ponderononon/IEMU_DevBoards/IEMU_Shared_Libraries/3D/TMUX1204DQAR.step

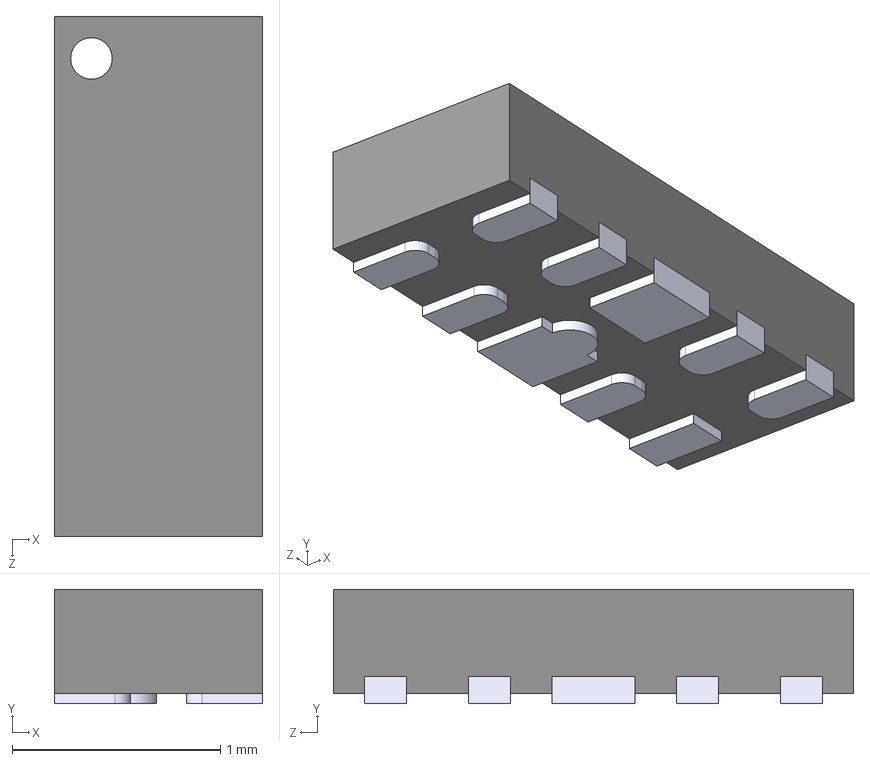
[picture p15: CAD file, 2026-05-08]
IEMU_Shared_Libraries/3D/TMUX1204DQAR.step
1.00 x 0.55 x 2.50 mm
