ponderononon/IEMU_DevBoards/IEMU_Shared_Libraries/3D/SJ3-35083B-TR.step

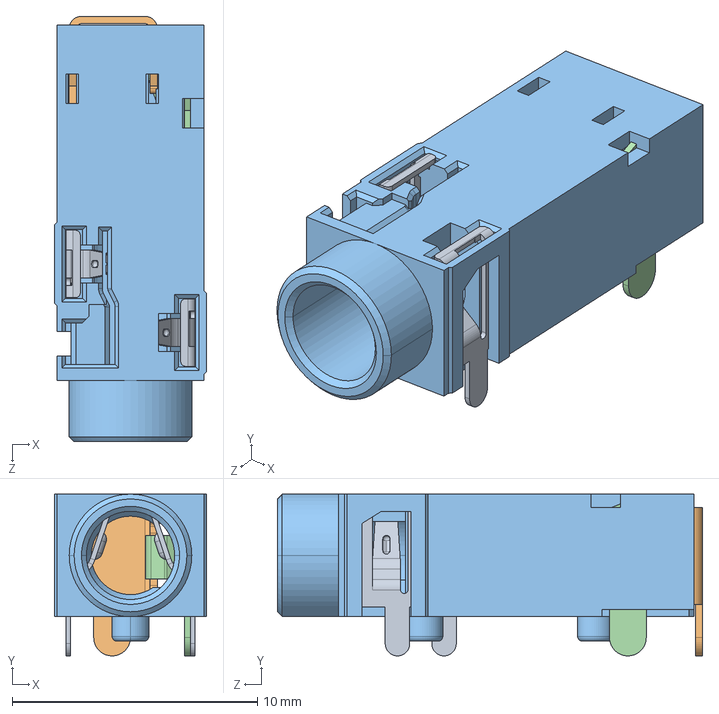
[picture p16: CAD file, 2026-05-08]
IEMU_Shared_Libraries/3D/SJ3-35083B-TR.step
6.20 x 6.60 x 17.3 mm
