ponderononon/IEMU_DevBoards/IEMU_Shared_Libraries/3D/NANOT160BP.stp

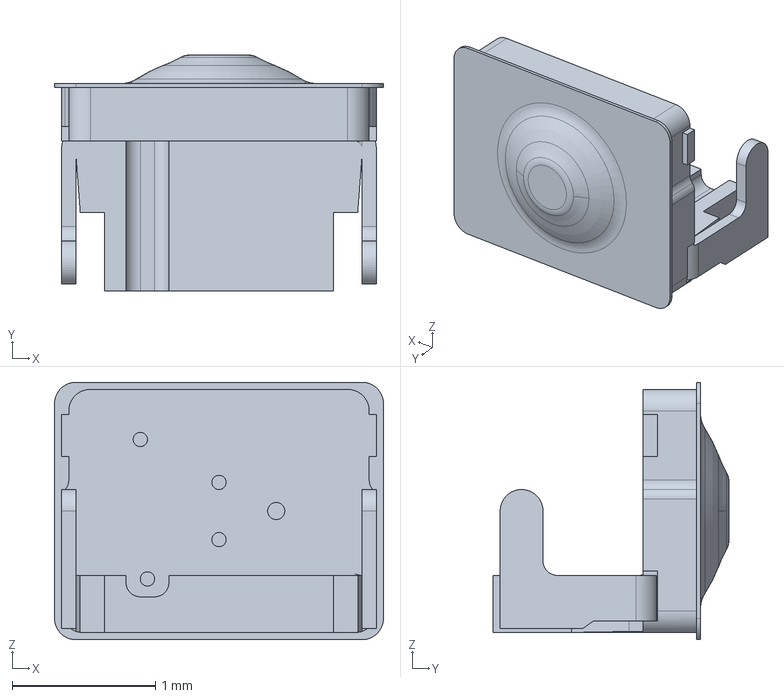
[picture p17: CAD file, 2026-05-08]
IEMU_Shared_Libraries/3D/NANOT160BP.stp
2.30 x 1.65 x 1.80 mm
