ponderononon/IEMU_DevBoards/IEMU_Shared_Libraries/3D/LTST-C19HE1WT.step

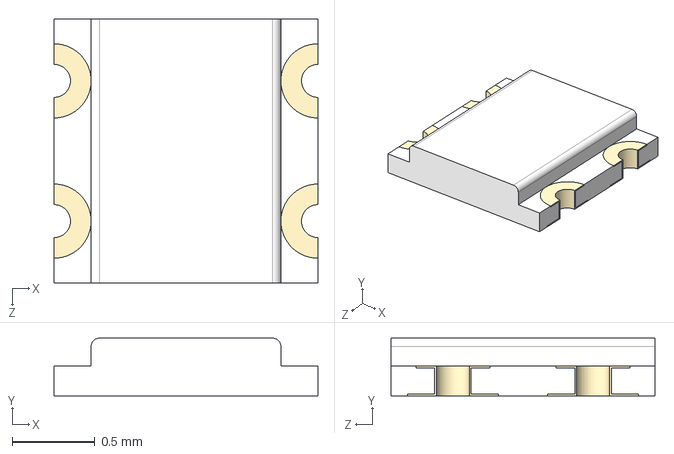
[picture p18: CAD file, 2026-05-08]
IEMU_Shared_Libraries/3D/LTST-C19HE1WT.step
1.60 x 0.35 x 1.60 mm
