ponderononon/IEMU_DevBoards/IEMU_Shared_Libraries/3D/VZ43FM1B8230001L.step

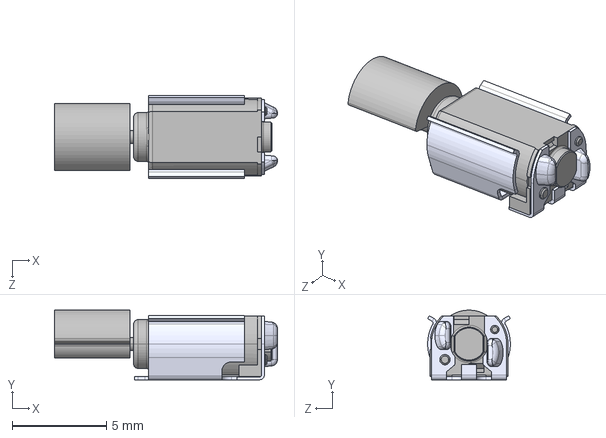
[picture p19: CAD file, 2026-05-08]
IEMU_Shared_Libraries/3D/VZ43FM1B8230001L.step
11.8 x 3.70 x 4.40 mm
