ponderononon/IEMU_DevBoards/IEMU_Shared_Libraries/3D/PMEG3010ESBYL.step

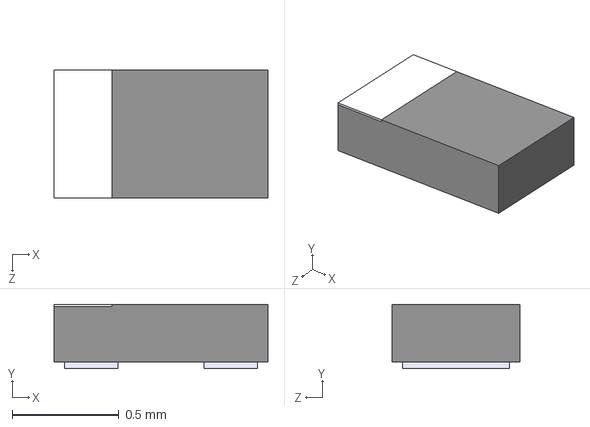
[picture p20: CAD file, 2026-05-08]
IEMU_Shared_Libraries/3D/PMEG3010ESBYL.step
1.00 x 0.3 x 0.6 mm
