ponderononon/IEMU_DevBoards/IEMU_Shared_Libraries/3D/USB4125-GF-A_REVA2.step

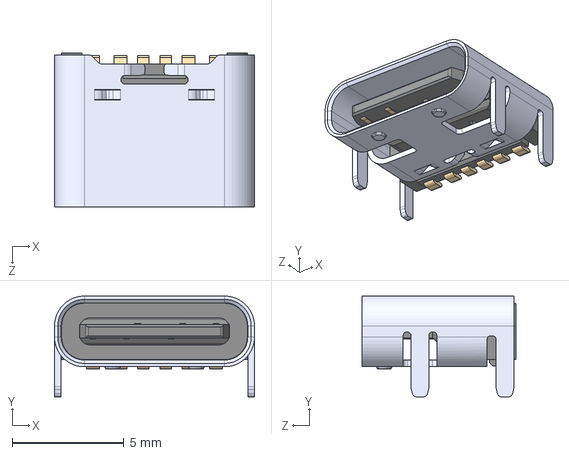
[picture p21: CAD file, 2026-05-08]
IEMU_Shared_Libraries/3D/USB4125-GF-A_REVA2.step
8.94 x 4.51 x 6.90 mm
