ponderononon/IEMU_DevBoards/IEMU_Shared_Libraries/3D/NPM1304-QEAA-R7.step

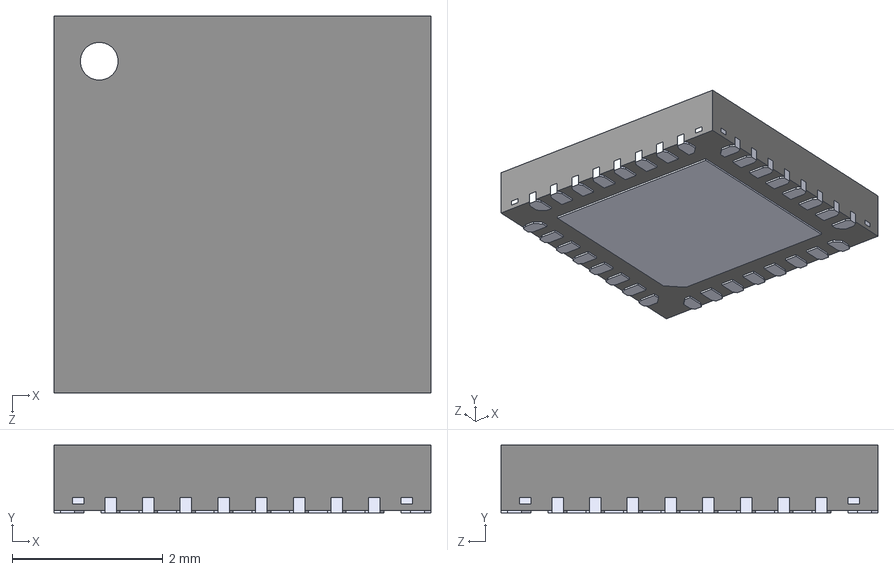
[picture p22: CAD file, 2026-05-08]
IEMU_Shared_Libraries/3D/NPM1304-QEAA-R7.step
5.00 x 0.9 x 5.00 mm
