ponderononon/IEMU_DevBoards/IEMU_Shared_Libraries/3D/W25N04KVZEIR.step

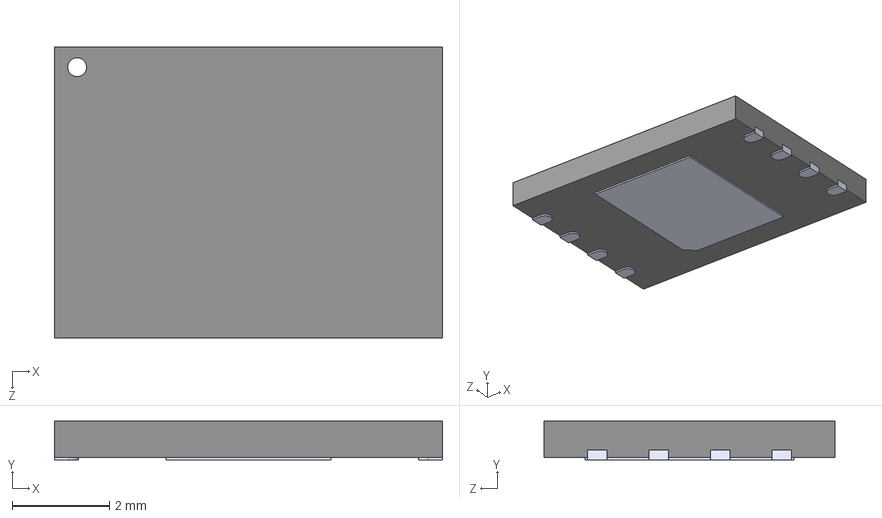
[picture p23: CAD file, 2026-05-08]
IEMU_Shared_Libraries/3D/W25N04KVZEIR.step
8.00 x 0.8 x 6.00 mm
