ponderononon/IEMU_DevBoards/IEMU_Shared_Libraries/3D/USB4215-03-A.stp

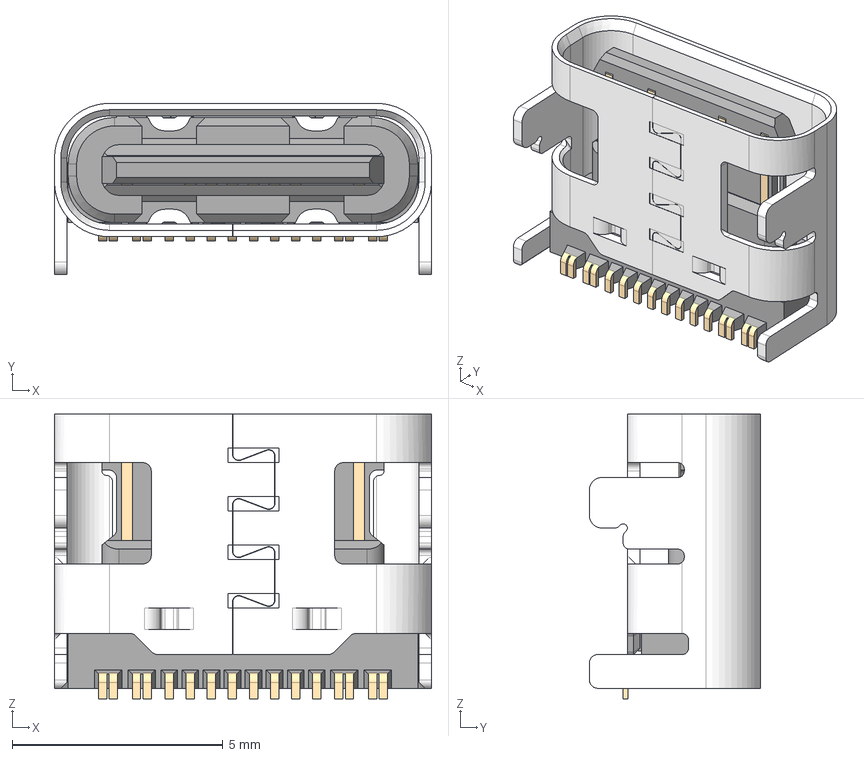
[picture p24: CAD file, 2026-05-08]
IEMU_Shared_Libraries/3D/USB4215-03-A.stp
8.94 x 4.06 x 6.75 mm
USB4215-03-A_PART1
USB4215-03-A_PART2
