ponderononon/IEMU_DevBoards/IEMU_Shared_Libraries/3D/TS-1088-AR02016.step

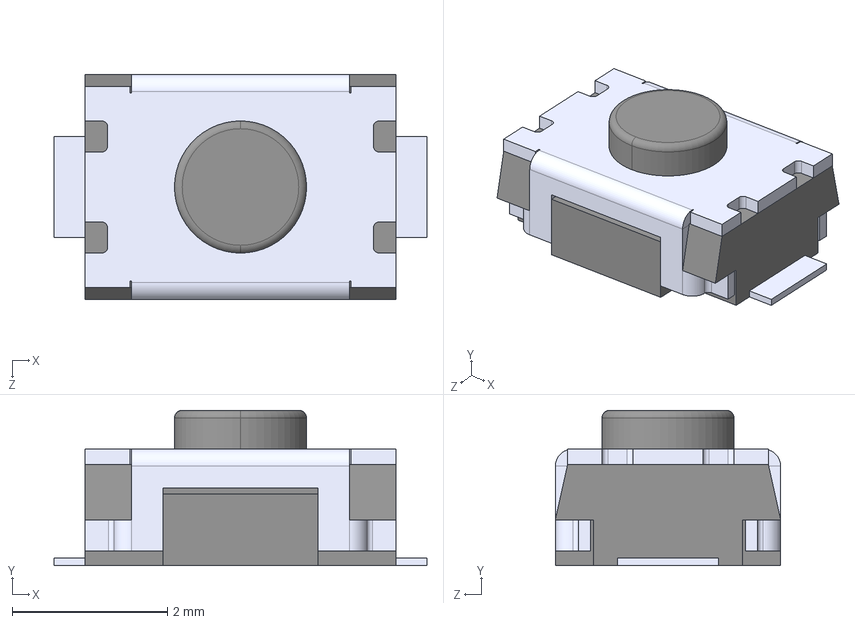
[picture p25: CAD file, 2026-05-08]
IEMU_Shared_Libraries/3D/TS-1088-AR02016.step
4.80 x 2.00 x 2.90 mm
