ponderononon/IEMU_DevBoards/IEMU_Shared_Libraries/3D/LTST-C191KRKT.step

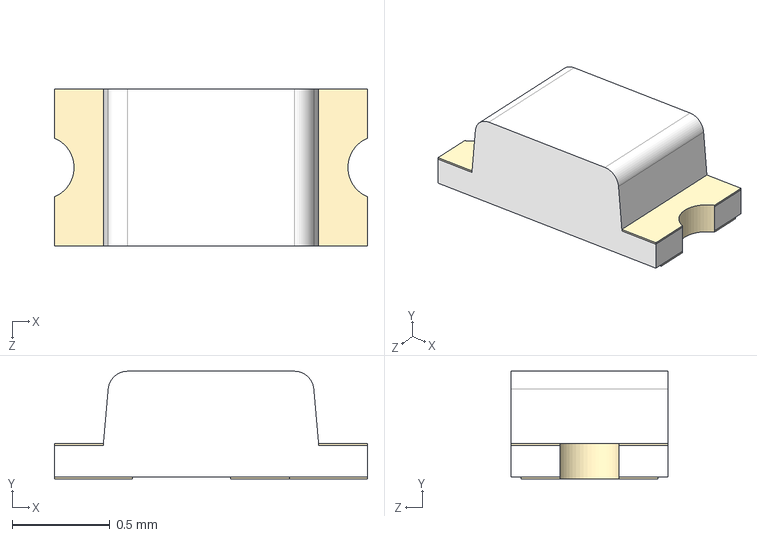
[picture p26: CAD file, 2026-05-08]
IEMU_Shared_Libraries/3D/LTST-C191KRKT.step
1.60 x 0.55 x 0.8 mm
