ponderononon/IEMU_DevBoards/IEMU_Shared_Libraries/3D/DF13-4P-1.25H_75_.step

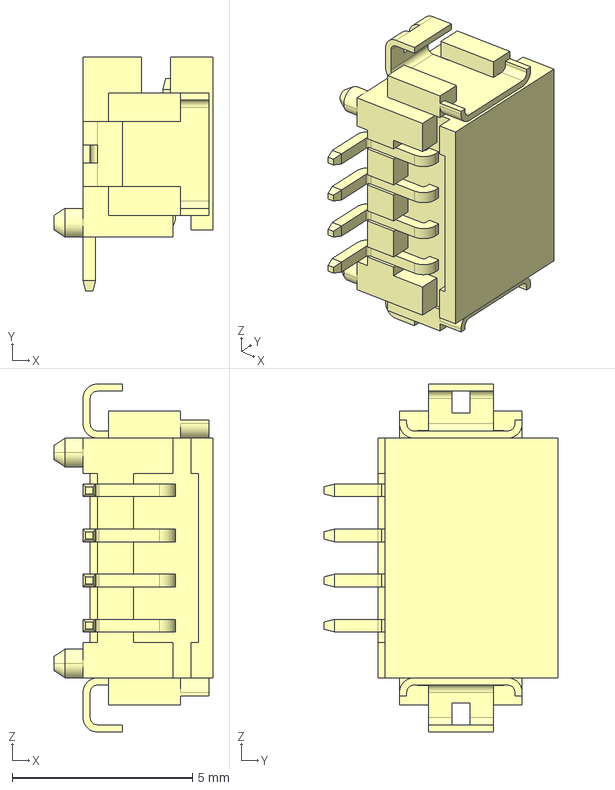
[picture p27: CAD file, 2026-05-08]
IEMU_Shared_Libraries/3D/DF13-4P-1.25H_75_.step
4.40 x 6.50 x 9.65 mm
